pemitharj/Sound-Reactive-Disco-Light-System/Design Files/Simulation/Schematic.asc

C1: cap; 0.0796µ
C2: cap; 0.0796µ
C3: cap; 0.63662µ
C4: cap; 0.63662µ
C5: cap; 63n
C6: cap; 63n
C7: cap; 0.63662µ
C8: cap; 0.63662µ
C9: cap; 47µ
C10: cap; 47µ
C11: cap; 47µ
C12: cap; 47µ
C13: cap; 47µ
C14: cap; 47µ
D1: diode
D2: diode
D3: diode
D4: diode
D5: diode
D6: diode
R1: res; 1k
R2: res; 1k
R3: res; 1k
R4: res; 1k
R5: res; 5k
R6: res; 5k
R7: res; 5k
R8: res; 5k
R9: res; 1k
R10: res; 1k
R11: res; 5k
R12: res; 5k
R13: res; 1k
R14: res; 1k
R15: res; 5k
R16: res; 5k
R17: res; 10k
R18: res; 100k
R19: res; 2k
R20: res; 2k
R21: res; 100k
R22: res; 10k
R23: res; 10k
R24: res; 100k
R25: res; 10k
R26: res; 100k
R27: res; 10k
R28: res; 10k
R29: res; 100k
R30: res; 10k
R31: res; 10k
R32: res; 8k
R33: res; 10k
R34: res; 8k
R35: res; 100k
R36: res; 100k
R37: res; 100k
R: res; 8k
U1: UniversalOpAmp2
U2: UniversalOpAmp2
U3: UniversalOpAmp2
U4: UniversalOpAmp2
U5: UniversalOpAmp2
U6: UniversalOpAmp2
U7: UniversalOpAmp2
U8: UniversalOpAmp2
U9: UniversalOpAmp2
U10: UniversalOpAmp2
U11: UniversalOpAmp2
V1: voltage; SINE(0 10m 1.5k); AC 1
V2: voltage; 6
V3: voltage; 3
V4: voltage; 3
V5: voltage; 3
Named nets: 0, V+, V-, Vout1, Vout2, Vout3
.tran 1
